crnicholson/Plant-Monitor/Code/embed/plantMonitor/lora.cpp

/*
lora.cpp, part of Plant Monitor, to monitor plant water levels.
Copyright (C) 2024 Charles Nicholson

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
You should have received a copy of the GNU General Public License
along with this program.  If not, see <https://www.gnu.org/licenses/>.
*/

#include "lora.h"

void loraSetup() {
  LoRa.setPins(CS, LORA_RESET, DIO0);

  if (!LoRa.begin(FREQUENCY)) {
#ifdef DEVMODE
    Serial.println("Starting LoRa failed!");
#endif
    while (1) {
      longBlink(LED);
    }
  }

#ifndef FAST_LORA
  LoRa.setSyncWord(SYNC_WORD);               // Defined in settings.h.
  LoRa.setSpreadingFactor(SPREADING_FACTOR); // Defined in settings.h.
  LoRa.setSignalBandwidth(BANDWIDTH);        // Defined in settings.h.
  LoRa.crc();                                // Checksum for packet error detection.
#endif

#ifdef FAST_LORA
  LoRa.setSyncWord(SYNC_WORD); // Defined in settings.h.
  LoRa.setSpreadingFactor(7);
  LoRa.setSignalBandwidth(250000);
  LoRa.crc(); // Checksum for packet error detection.
#endif
}

void sendData(struct data &newPacket) {
  while (LoRa.beginPacket() == 0) {
    delay(10);
  }

  LoRa.beginPacket();

  byte *packetBytes = (byte *)&newPacket;
  for (int i = 0; i < sizeof(newPacket); i++) {
    byte encodedByte = hammingEncode(packetBytes[i]);
    LoRa.write(encodedByte);
  }

  LoRa.endPacket(); // Don't use async send. This also sends the data.

#ifdef CHANGE_TX_POWER
  if (newPacket.requestRSSI) {
    while (LoRa.parsePacket() < 0) {
      longBlink(LED);
#ifdef DEVMODE
      Serial.println("Requested RSSI, waiting for response.");
#endif
      long receivedID;
      long receivedRSSI;
      lora.readBytes((byte *)&receivedID, sizeof(long));
      lora.readBytes((byte *)&receivedRSSI, sizeof(long));
      if (receivedID == DEVICE_ID) {
#ifdef DEVMODE
        Serial.println("Received ID matches the device ID.");
        Serial.print("RSSI: ");
        Serial.println(receivedRSSI);
#endif
        adjustTXPower(receivedRSSI);
      } else {
#ifdef DEVMODE
        Serial.println("Received ID does not match the device ID.");
#endif
        longBlink(LED);
      }
    }
  }
#endif

  LoRa.end(); // This is supposedly better than LoRa.sleep().
}

byte hammingEncode(byte data) {
  byte p1 = ((data >> 2) & 0x1) ^ ((data >> 1) & 0x1) ^ ((data >> 0) & 0x1);
  byte p2 = ((data >> 3) & 0x1) ^ ((data >> 1) & 0x1) ^ ((data >> 0) & 0x1);
  byte p3 = ((data >> 3) & 0x1) ^ ((data >> 2) & 0x1) ^ ((data >> 0) & 0x1);

  byte hamming = (p1 << 6) | (p2 << 5) | (p3 << 4) | (data & 0xF);
  return hamming;
}

void sendForRSSI() {
  while (LoRa.beginPacket() == 0) {
    delay(10);
  }

  LoRa.beginPacket();
  LoRa.write((byte *)&DEVICE_ID, sizeof(long));
  LoRa.endPacket(); // Don't use async send.
  while (LoRa.parsePacket() < 0) {
    longBlink(LED);
#ifdef DEVMODE
    Serial.println("Sending for RSSI, waiting for response.");
#endif
    long receivedID;
    long receivedRSSI;
    lora.readBytes((byte *)&receivedID, sizeof(long));
    lora.readBytes((byte *)&receivedRSSI, sizeof(long));
    if (receivedID == DEVICE_ID) {
#ifdef DEVMODE
      Serial.println("Received ID matches the device ID.");
      Serial.print("RSSI: ");
      Serial.println(receivedRSSI);
#endif
      adjustTXPower(receivedRSSI);
    } else {
#ifdef DEVMODE
      Serial.println("Received ID does not match the device ID.");
#endif
      longBlink(LED);
    }
  }
}

void receiveRSSI() {
  int packetSize = LoRa.parsePacket(); // Parse packet.

  if (packetSize > 0) {
    LoRa.readBytes(receivedBytes, sizeof(long));
  }
}

// This adjusts the power of the LoRa module to save power in general.
void adjustTXPower(int rssi) {
  if (rssi > RSSI_THRESHOLD_HIGH) {
    LoRa.setTxPower(5); // Lower power for strong signal.
  } else if (rssi >) {
    LoRa.setTxPower(10); // Medium power for moderate signal.
  } else {
    LoRa.setTxPower(20); // Maximum power for weak signal.
  }
#ifdef DEVMODE
  Serial.print("RSSI: ");
  Serial.print(rssi);
  Serial.print(" dBm, TX power: ");
  Serial.print(LoRa.getTxPower());
  Serial.println(" dBm");
#endif
}
